Dacetylan/FLWSB/docs/demo/flwsb-demo.md

# DEMO

## FLWSB

Demo opstelling van de SAMDaaNo21 PoC met BME280 breakoutboard op breadboard.
Gevoed door de Solar Power Manager met twee kleine zonnepanelen en heroplaadbare Li-Po batterij.

### Overzicht

FLWSB demo opstellig: overzicht, hoek. Figuur 1: FLWSB demo opstellig: overzicht, hoek..

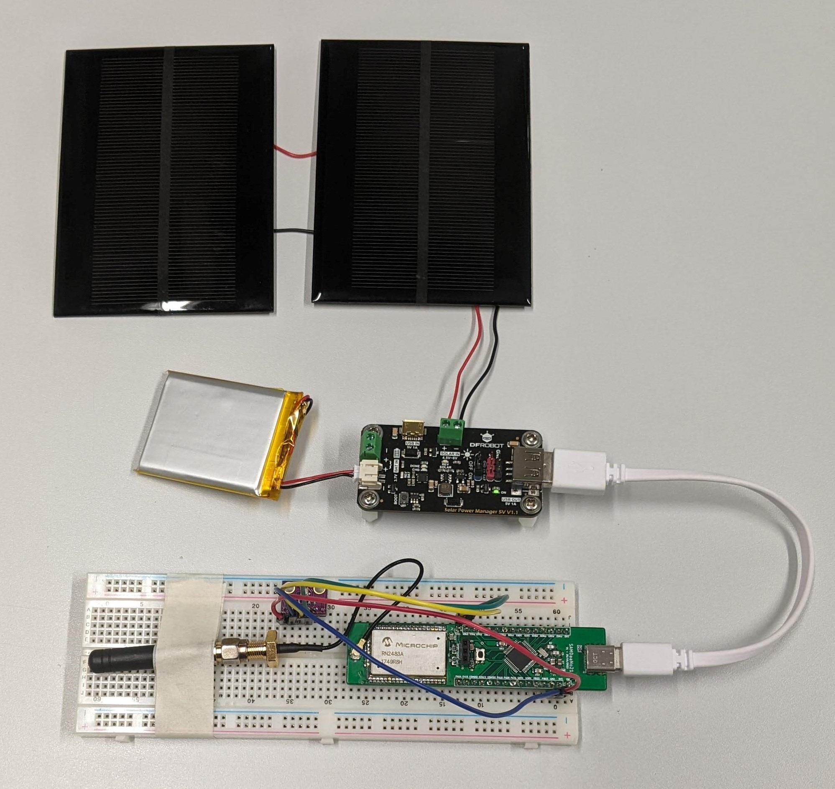
[picture p45: docs/demo/assets/flwsb-demo-overview-top.jpg]
FLWSB demo opstellig: overzicht, bovenaanzicht. Figuur 2: FLWSB demo opstellig: overzicht, bovenaanzicht..


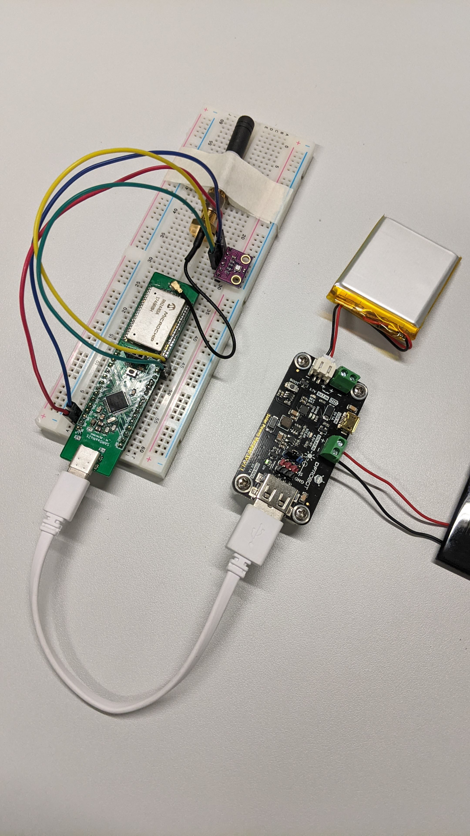
[picture p46: docs/demo/assets/flwsb-demo-overview-woSolar-angle.jpg]
FLWSB demo opstellig: overzicht, hoek, zonder zonnepanelen. Figuur 3: FLWSB demo opstellig: overzicht, hoek, zonder zonnepanelen..


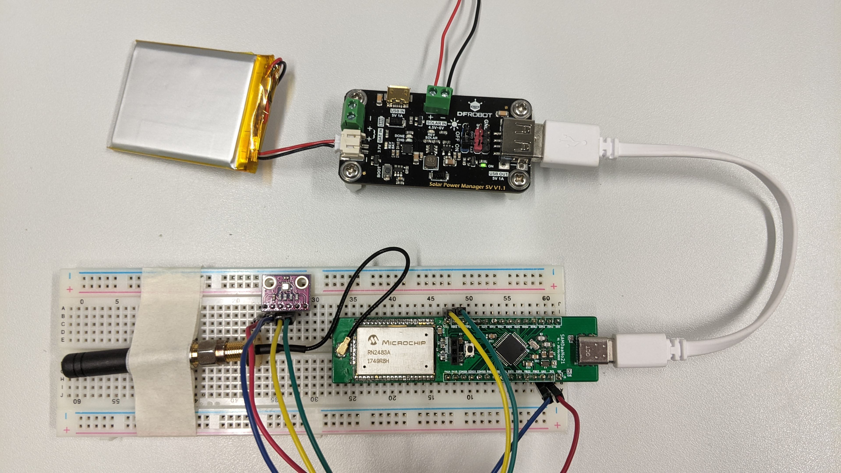
[picture p47: docs/demo/assets/flwsb-demo-overview-woSolar-top.jpg]
FLWSB demo opstellig: overzicht, top, zonder zonnepanelen. Figuur 4: FLWSB demo opstellig: overzicht, top, zonder zonnepanelen..


### Solar Power Manager met Li-Po batterij en zonnepanelen

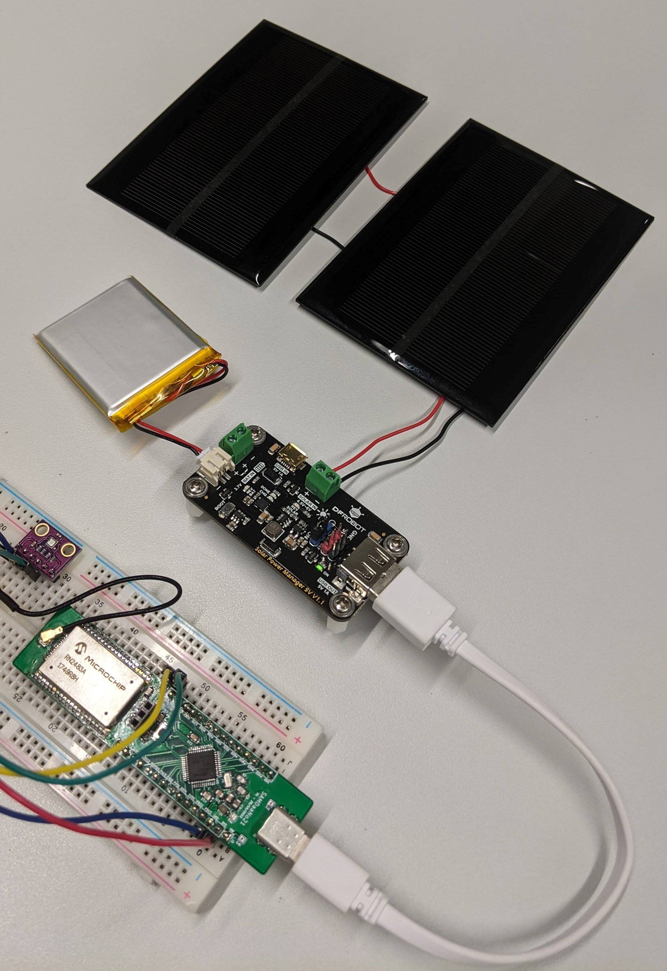
[picture p48: docs/demo/assets/flwsb-demo-solar-angle.jpg]
FLWSB demo opstellig: Solar Power Manager met Li-Po batterij en zonnepanelen, hoek. Figuur 5: FLWSB demo opstellig: Solar Power Manager met Li-Po batterij en zonnepanelen, hoek..


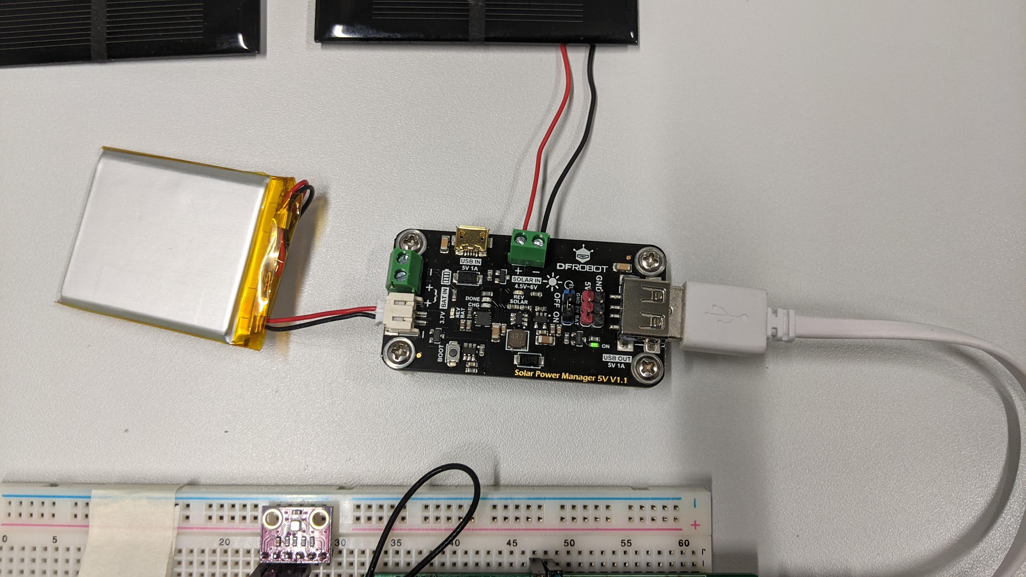
[picture p49: docs/demo/assets/flwsb-demo-solar-top.jpg]
FLWSB demo opstellig: Solar Power Manager met Li-Po batterij en zonnepanelen, bovenaanzicht. Figuur 6: FLWSB demo opstellig: Solar Power Manager met Li-Po batterij en zonnepanelen, bovenaanzicht..


### SAMDaaNo21

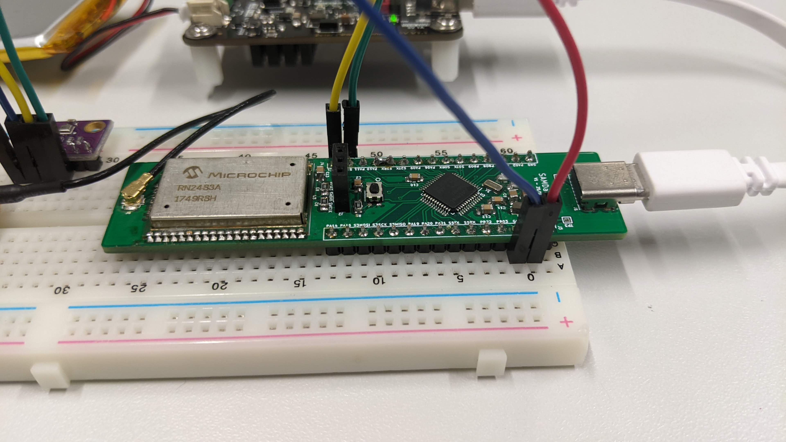
[picture p50: docs/demo/assets/flwsb-demo-samdaano21-close-up-side.jpg]
FLWSB demo opstellig: SAMDaaNo21, zijdelinks. Figuur 7: FLWSB demo opstellig: SAMDaaNo21, zijdelinks..


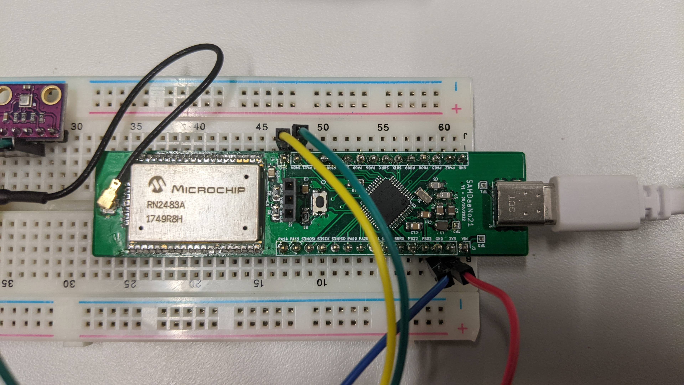
[picture p51: docs/demo/assets/flwsb-demo-samdaano21-close-up-top.jpg]
FLWSB demo opstellig: SAMDaaNo21, bovenaanzicht. Figuur 8: FLWSB demo opstellig: SAMDaaNo21, bovenaanzicht..


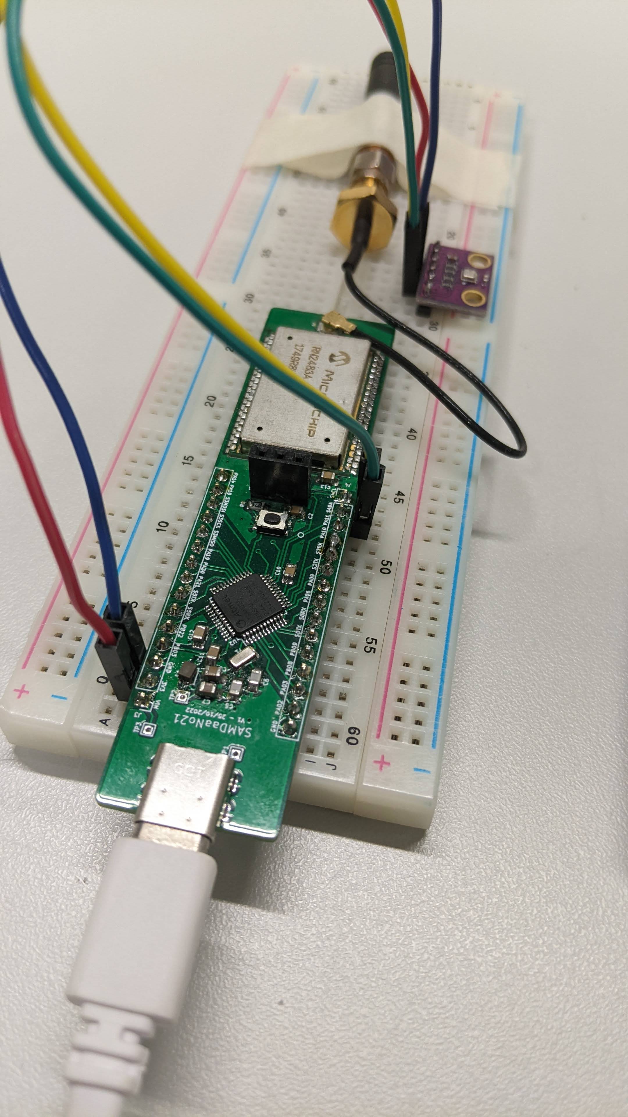
[picture p52: docs/demo/assets/flwsb-demo-samdaano21-close-up-angle.jpg]
FLWSB demo opstellig: SAMDaaNo21, hoek. Figuur 9: FLWSB demo opstellig: SAMDaaNo21, hoek..


### BME280 breakoutboard

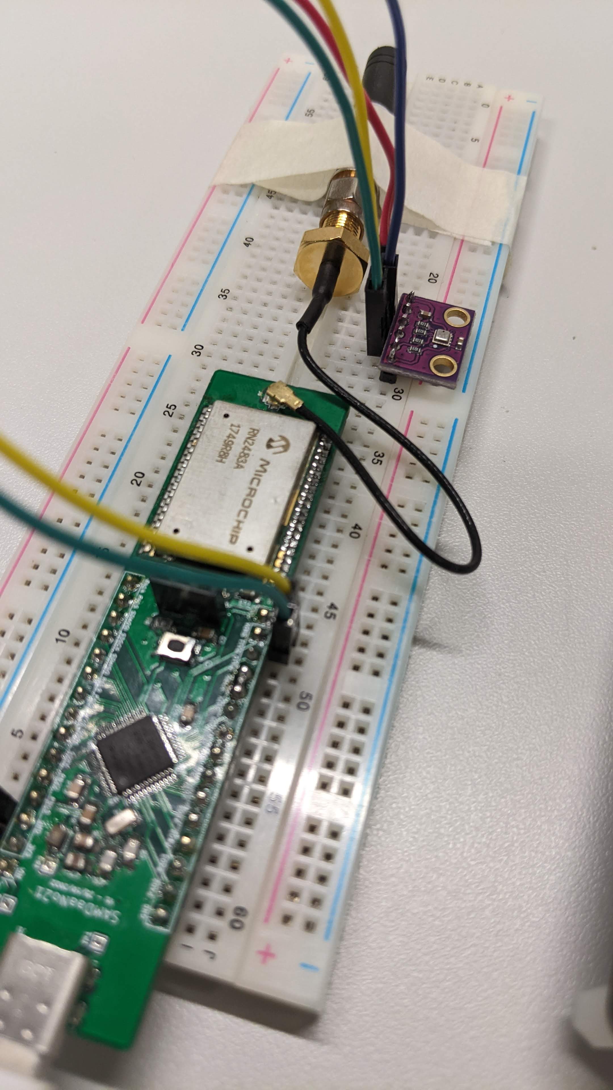
[picture p53: docs/demo/assets/flwsb-demo-bme280-close-up-angle.jpg]
FLWSB demo opstellig: BME280 breakoutboard, hoek. Figuur 10: FLWSB demo opstellig: BME280 breakoutboard, hoek..


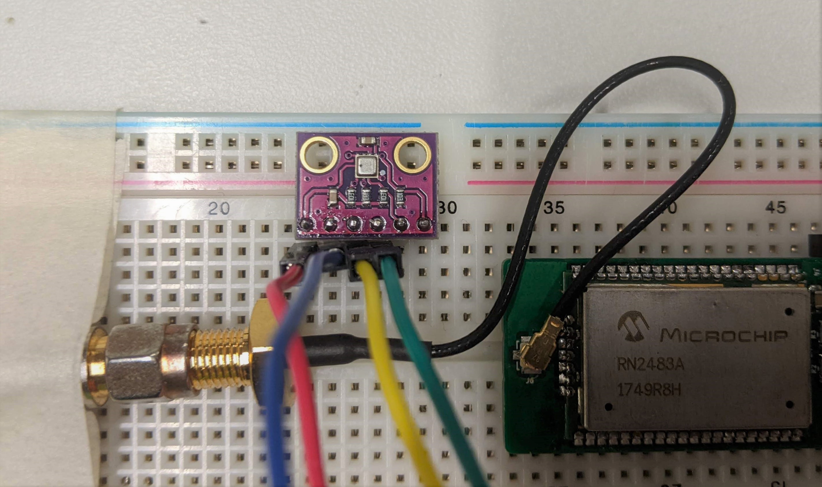
[picture p54: docs/demo/assets/flwsb-demo-bme280-close-up-top.jpg]
FLWSB demo opstellig: BME280 breakoutboard, bovenaanzicht. Figuur 11: FLWSB demo opstellig: BME280 breakoutboard, bovenaanzicht..
