Dacetylan/FLWSB/docs/enclosure/considerations.md

# Behuizing

## Overwegingen

### Introductie

De behuizing zelf is geen onderdeel van deze itteratie van het project. Bij het ontwikkelen van de PCB's is het echter belangrijk al na te denken over hoe deze geplaatst zal worden. Zeker omdat het doel is om dit project uit te rollen in Sub-Sahara Afrika wat een zeer andere omgeving is als West-Europa. Meer specifiek in Zanzibar, Tanzania en Ghana.

Er zal gebruik gemaakt worden van __zonne-energie__ aan de hand van zonnepanelen waar een aantal factoren bij komen kijken.
Factoren waarbij er rekening moet gehouden worden bij het plaatsen van zonne-panelen in Sub-Sahara Afrika:
- Kantelhoek (tilt angle) van het zonnepaneel
- Oriëntatie van het zonnenpaneel
- Afzetting van Harmattan dust
- Afwatering van regenwater
- Temperatuur van het zonnenpaneel

Andere factoren waar rekening mee gehouden moet worden zijn algemen zaken bij het opmeten van __klimatologische data__ zoals:
- Lucht toe voer naar sensoren voor lucht en deeltjes analyse.
- Stof filtering van grote stofdeeltjes groter dan 10 micron.
- Invloed van opwarmende componenten voor temperatuur metingen en dus koeling.
- Afdekking van de elektronica tegen vocht en regen.

In dit hoofdstuk worden deze factoren verder besproken.
