Dacetylan/FLWSB/docs/enclosure/measuring-climate.md

# Behuizing

## Klimatologische metingen

Voor het meten van klimatologische data moet er rekening gehouden worden met een aantal factoren zoals:
- Lucht toe voer naar sensoren voor lucht en deeltjes analyse.
- Stof filtering van grote stofdeeltjes groter dan 10 micron.
- Invloed van opwarmende componenten voor temperatuur metingen en dus koeling.
- Afdekking van de elektronica tegen vocht en regen.

### Stevenson Screen

### Bestaande behuizingen

#### Off-the-shelf behuizingen

#### 3D Printing
