Dacetylan/FLWSB/docs/frontend/Documentatie Frontend.md

# Documentatie Frontend

### Mock up

Voor dat het mogelijk is om te beginnen met het ontwerpen van de frontend moet er een mock up gemaakt worden. Voor de frontend zijn er twee onderdelen. Een Sensor Registration Form en een grafische weergave van de data.

Screenshot 2022-09-30 at 11.58.03.png

*fig. 1, Sensor Registration Form Mock up*



*fig. 2, Grafana wordt gebruikt voor een grafische weergave van de data*

### Sensor Registration Form

De eerste versie van de Sensor Registration Form werd ontworpen met Angular. Angular werd gebruik omdat dit de techniek is dat aangeleerd werd tijdens de lessen Web Frameworks.

Screenshot 2022-10-28 at 10.28.20.png

*fig. 3, eerste versie Sensor Regiostration Form*

Angular is heel inefficiënt en eigenlijk helemaal niet leuk om mee te werken. We hebben voor de tweede versie besloten om gebruik te maken van NodeRED Dashboard voor de Sensor Registration Form. NodeRED wordt al gebruikt voor de backend. Zo moeten we geen nieuwe Docker container opstarten voor een simpele form. Deze tweede versie is nog niet gebouwd.
