Dacetylan/FLWSB/docs/backend/influxdb.md

# Backend

## InfluxDb Time-Series Database

Voor dit project is er gekozen om te werken met InfluxDb.
Dit is een time-series database, wat wilt zeggen dat aan alle datapunten een timestamp, of datum en tijdstip is gekoppeld. Dit maakt het uitermate geschikt om historische data te verzamelen en deze om te zetten in grafieken. Ideaal dus voor klimatologische data zoals in dit project.

De keuze voor deze database ligt ook bij onze keuze voor het gebruik van Grafana als frontend visualisatie van de verzamelde data. Grafana beschikt over een eenvoudige, en gratis, plug-in die de verbinding tussen de twee super simpel maakt om op te zetten.

Enkele specificaties:
- InfluxDb 2.0
- Open-source Time Series Database (TSDB)
- geschreven in GO programeertaal
- Flux query-taal

[Officiële documentatie website](https://www.influxdata.com/_resources/)

Voordelen:
- Zeer performant in queriën van zeer grote hoeveelheden data.
- Wanneer geschreven wordt naar de database werkt dit het beste in grote blokken data in één keer.
- Zeer eenvoudig data op te vragen door schema systeem (zie Schema Design onderaan) met tags.

---

### Werking

InfluxDb beschikt over een CLI, maar kan ook eenvoudig beheerd worden aan de hand een web interface.

#### Buckets

Buckets zijn eenvoudig te beheren.

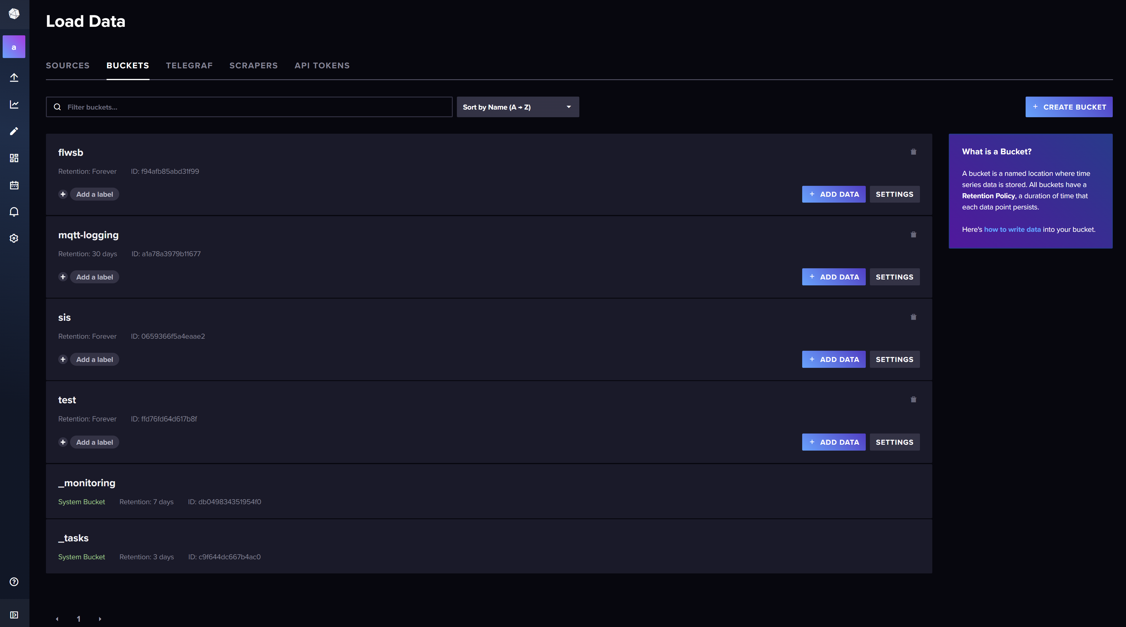
[picture p68: docs/backend/assets/influxdb-buckets.png]
InfluxDb web interface: Buckets. Figuur 1: InfluxDb web interface: Buckets.


#### API Tokens

API tokens aanmaken, om connecties naar buiten op te zetten, met specifieke machtigingen kunnen ook zeer eenvoudig.

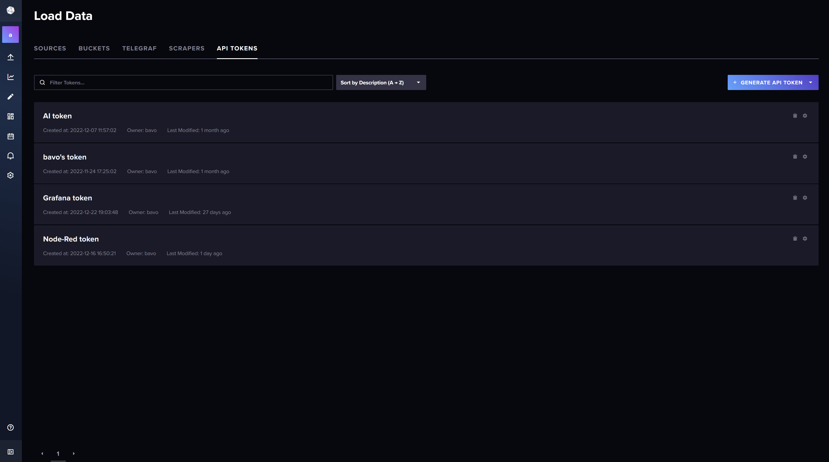
[picture p69: docs/backend/assets/influxdb-api-tokens.png]
InfluxDb web interface: API tokens. Figuur 2: InfluxDb web interface: API tokens.


#### Data Explorer

De web interface beschikt ook over een Data Explorer. Een zeer handige tool om query's op te stellen, als ook een snelle visualisatie van data.

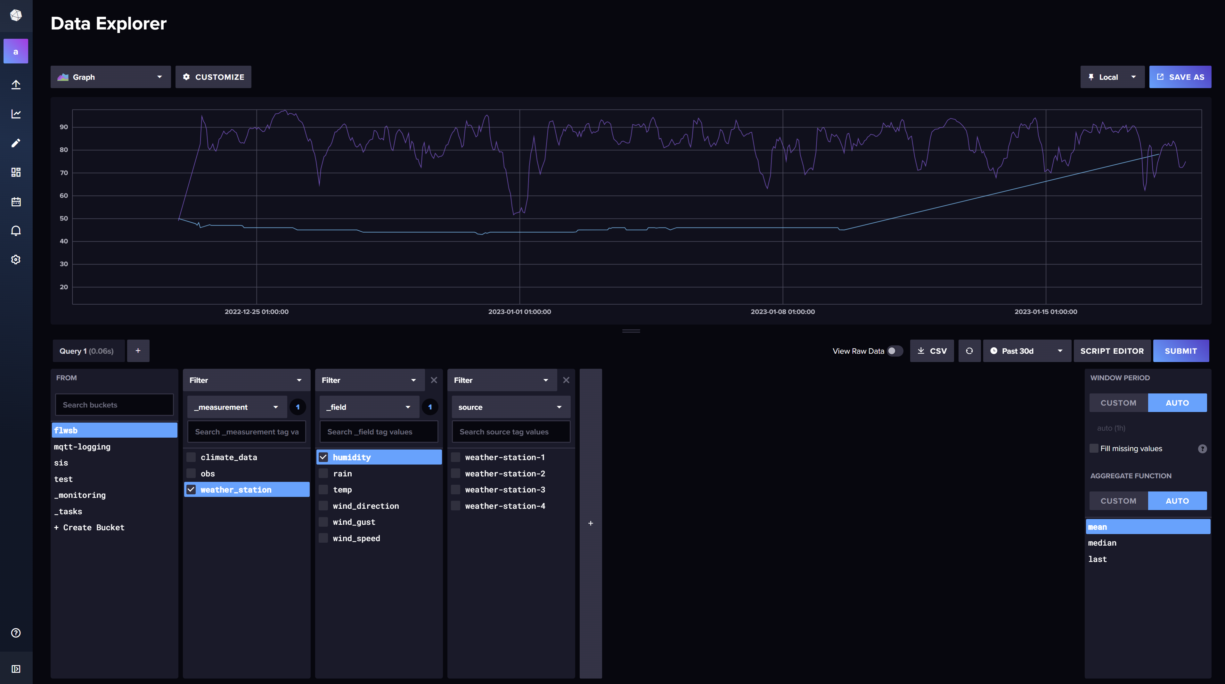
[picture p70: docs/backend/assets/influxdb-data-explorer-query-builder-graph.png]
InfluxDb web interface: Data Explorer, Query Builder en graph view. Figuur 3: InfluxDb web interface: Data Explorer, Query Builder en graph.


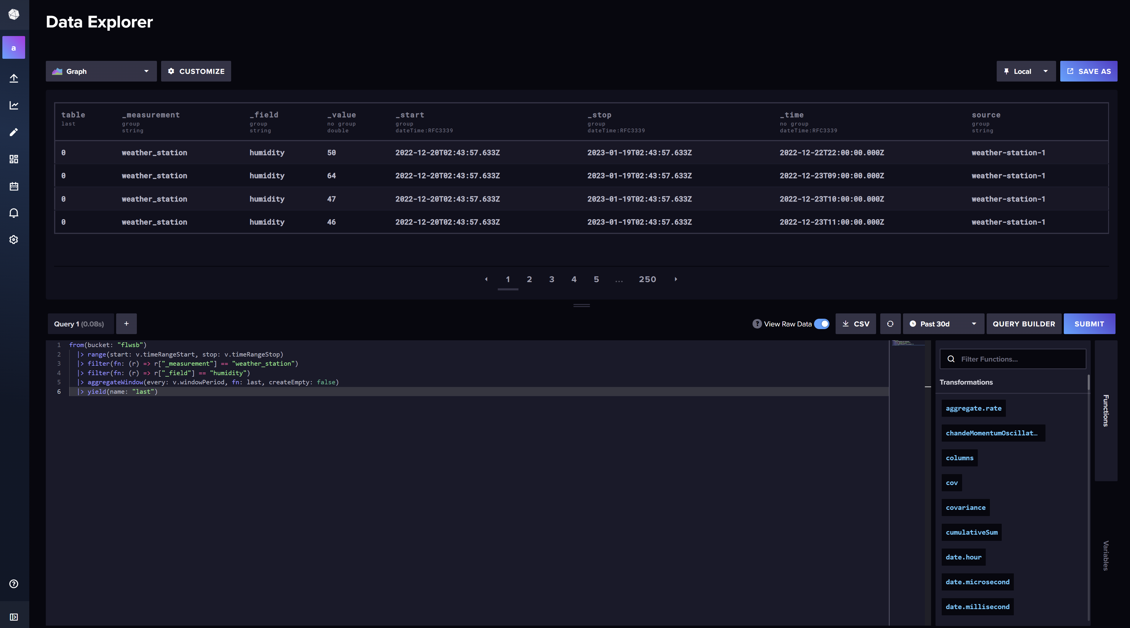
[picture p71: docs/backend/assets/influxdb-data-explorer-script-editor-raw-data.png]
InfluxDb web interface: Data Explorer, Script Editor en raw data view. Figuur 4: InfluxDb web interface: Data Explorer, Script Editor en raw data view.


---

### Schema Design

De InfluxDb documentatie heeft een onderdeel over InfluxDb schema design onder [Write data - Best practices- Schema design](https://docs.influxdata.com/influxdb/v2.4/write-data/best-practices/schema-design/).

InfluxDb bestaat uit volgende onderdelen:

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

_**Keys** herhalen niet binnen een schema en kunnen geen gereserveerde keywords zijn of speciale tekens bevatten._

_**Measurements** en **keys** bevatten geen data; **tag values** en **field values** bevatten wel data._

_Een **datapunt / point** bevat een series key, een field value en een timestamp.
vb. ```2019-08-18T00:00:00Z census ants 30 portland mullen```. Waarbij measurement = census, field key = ants, field value = 30, location tag = portland, en scientist tag = mullen._

_Een **series key** is een collectie van datapunten dat een measurement, tag set en field key delen.
Een **series** bevat timestamps en field values voor een bepaalde series key._

[_Bron: InlfuxDb data elements_](https://docs.influxdata.com/influxdb/cloud/reference/key-concepts/data-elements/#bucket)

<br>
