Dacetylan/FLWSB/docs/frontend/dashboard.md

# Frontend

## Node-RED Dashboard

Als invoer manier voor het Sensor Identification System (SIS) wordt er gebruik gemaakt van Node-RED Dashboard. Dit genereerd een eenvoudige web pagina met de nodige formulieren.
De werking hiervan is gedocumenteerd in het onderdeel [Node-RED](backend/nodered.md) onder Backend.

SIS Registration Form webpagina. Figuur 1: SIS Registration Form webpagina.

Met voorbeeld data ingevuld:

SIS web forms voorbeeld. Figuur 2: SIS web forms voorbeeld.
