Dacetylan/FLWSB/docs/demo/weather-station-demo.md

# DEMO

# Weerstation

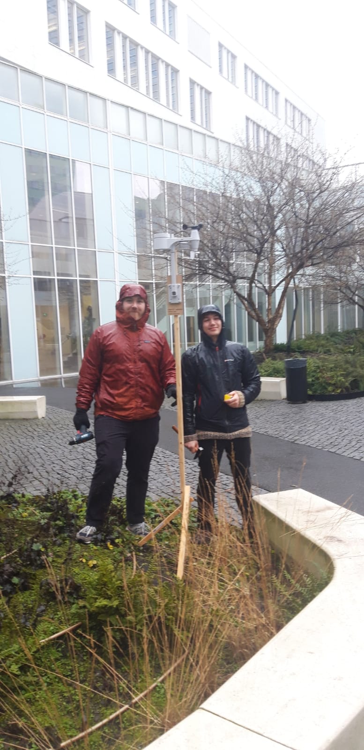
[picture p80: docs/demo/assets/weather-station-demo-birk-luyts.jpeg]
Buiten opstelling van demo weerstation met Maarten Luyts links en Birk Tamm rechts, dag 1. Figuur 1: Buiten opstelling van demo weerstation met Maarten Luyts links en Birk Tamm rechts, dag 1.


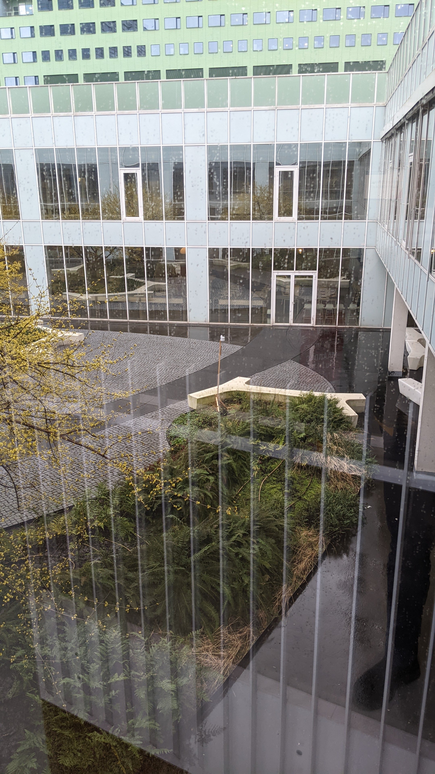
[picture p81: docs/demo/assets/weather-station-demo-1.jpg]
Buiten opstelling van demo weerstation, een maand later. Figuur 2: Buiten opstelling van demo weerstation, een maand later.


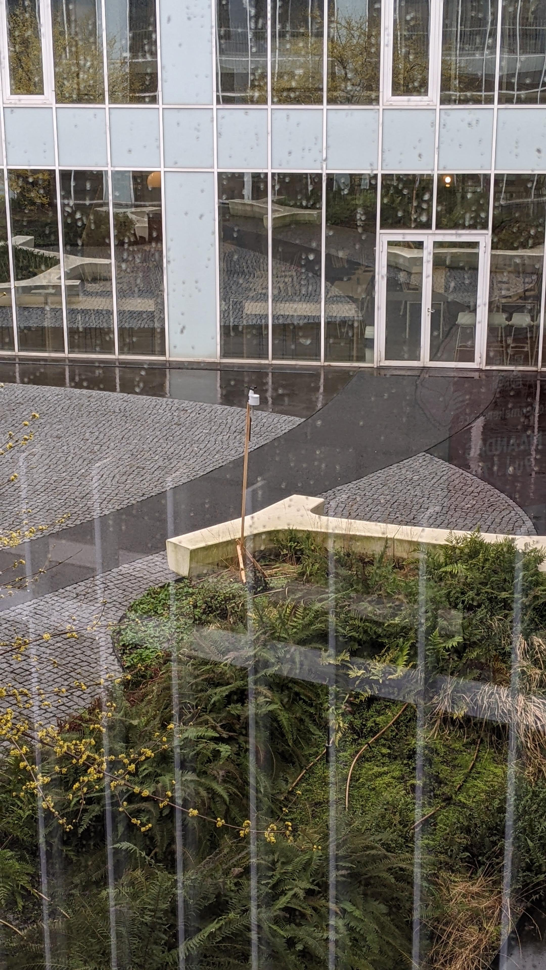
[picture p82: docs/demo/assets/weather-station-demo-2.jpg]
Buiten opstelling van demo weerstation, een maand later (zoom). Figuur 3: Buiten opstelling van demo weerstation, een maand later (zoom).


Buiten opstelling van demo weerstation, een maand later (extra zoom). Figuur 4: Buiten opstelling van demo weerstation, een maand later (extra zoom).
