Dacetylan/FLWSB/docs/backend/assets/grafana-dashboard-weather-stations.png

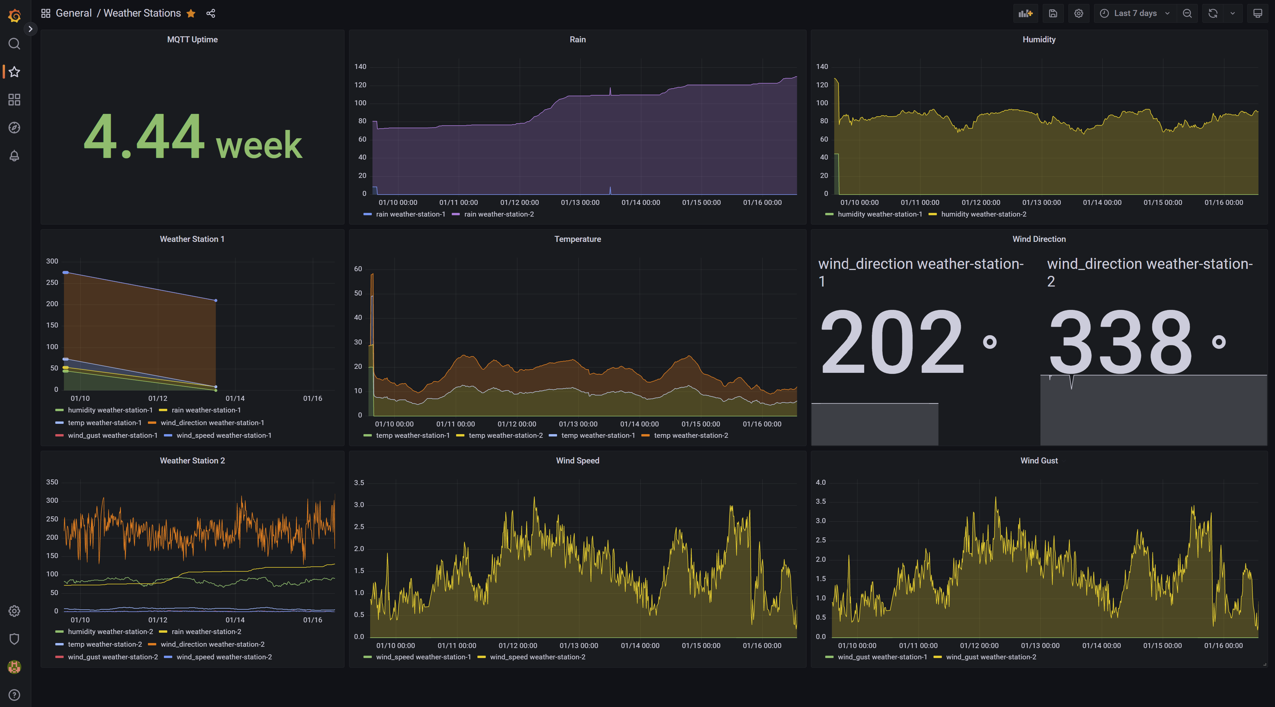
docs/backend/assets/grafana-dashboard-weather-stations.png
