Dacetylan/FLWSB/docs/backend/assets/ttn-collaborators.png

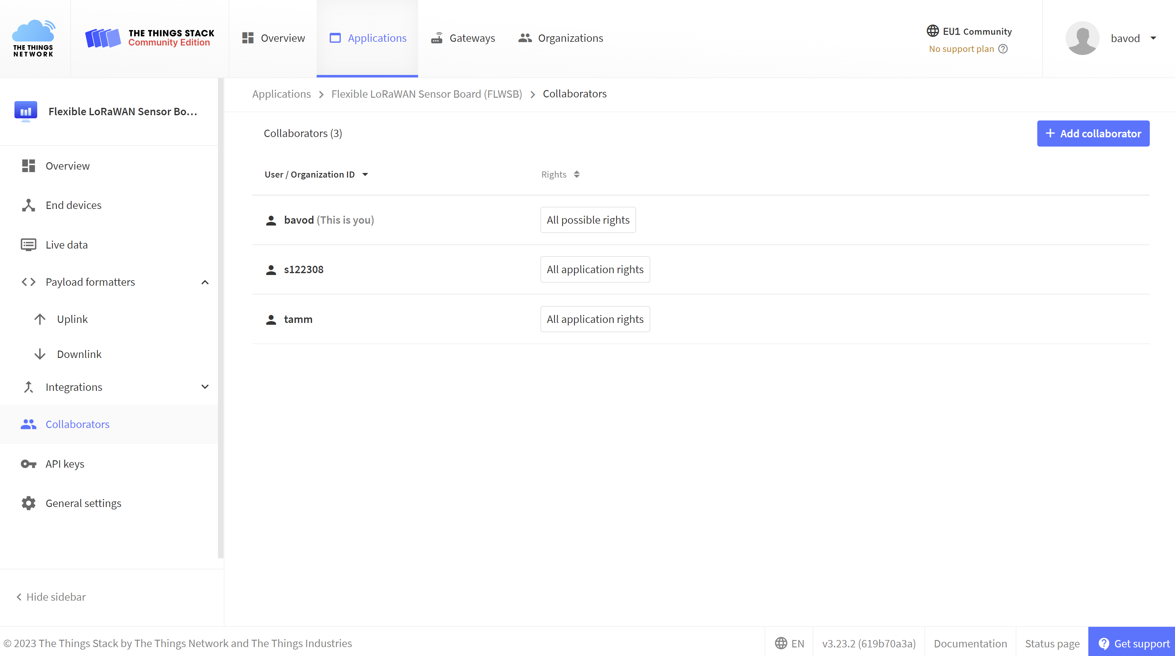
docs/backend/assets/ttn-collaborators.png
