Dacetylan/FLWSB/docs/backend/assets/ttn-id.png

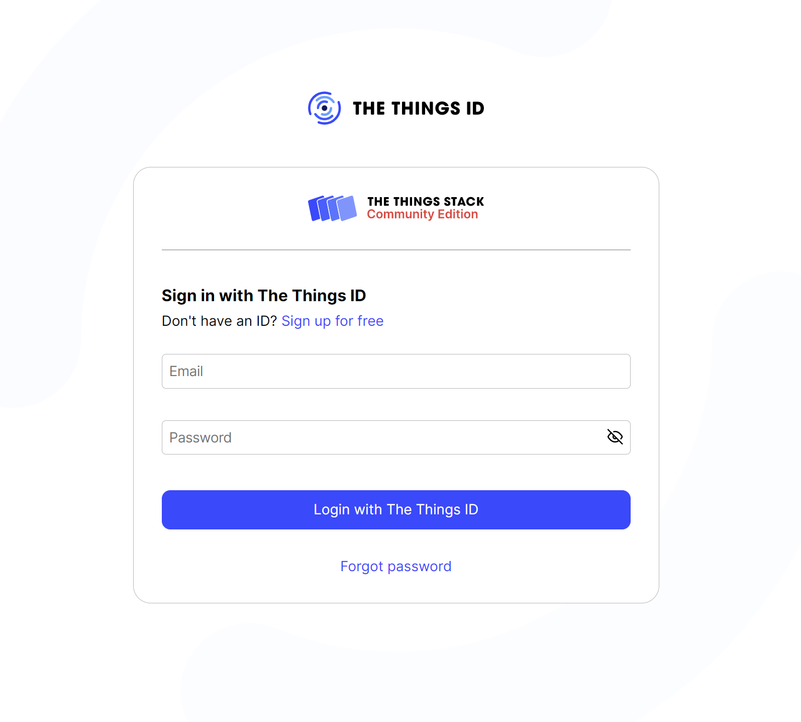
docs/backend/assets/ttn-id.png
