Dacetylan/FLWSB/docs/data-formatting/assets/node-red-flow-ttn-flwsb.png

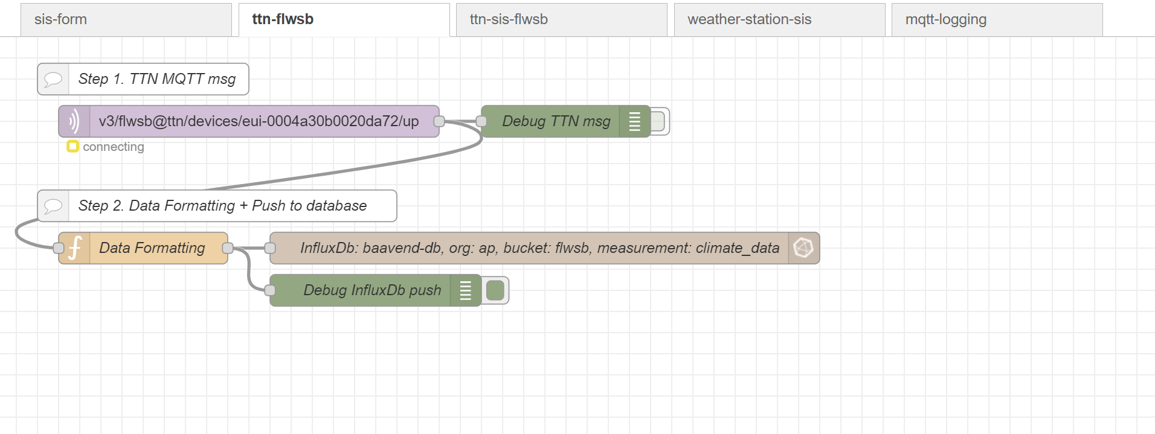
docs/data-formatting/assets/node-red-flow-ttn-flwsb.png
