Dacetylan/FLWSB/docs/data-formatting/assets/node-red-flow-weather-station.png

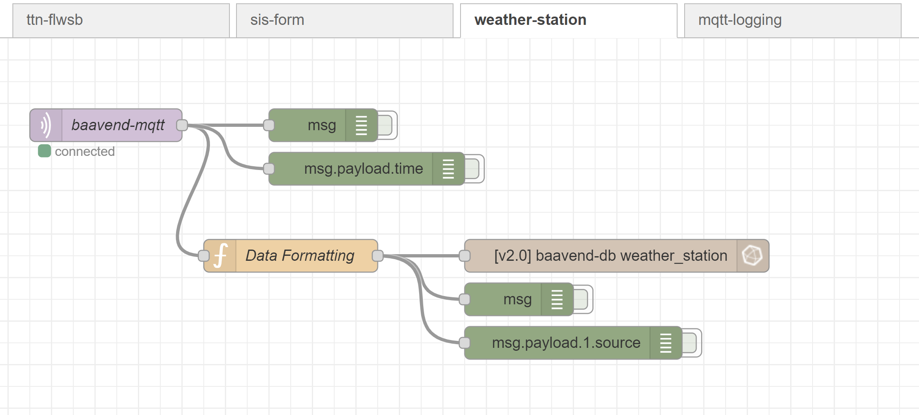
docs/data-formatting/assets/node-red-flow-weather-station.png
