Dacetylan/FLWSB/docs/data-formatting/assets/zanzibar/formatted-msg.png

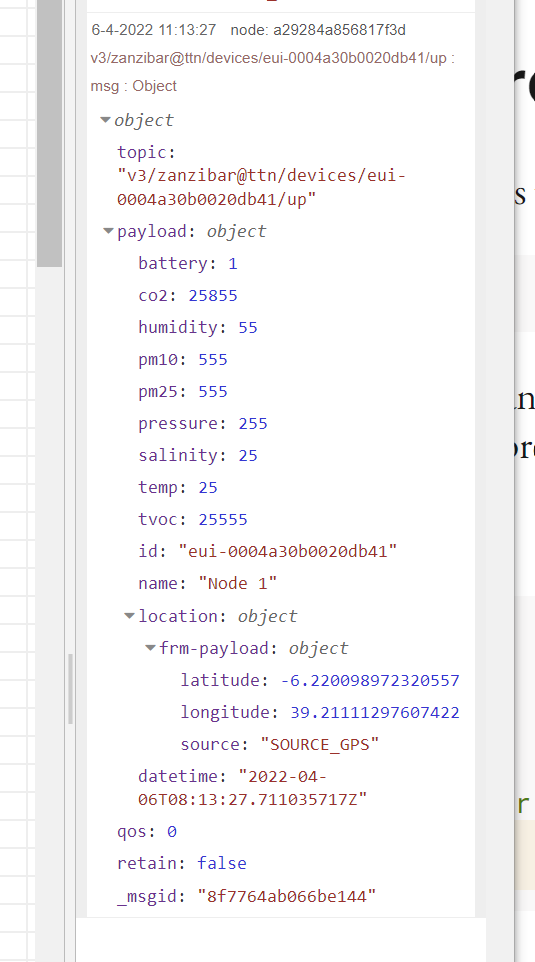
docs/data-formatting/assets/zanzibar/formatted-msg.png
