Dacetylan/FLWSB/docs/data-formatting/assets/zanzibar/node-red-function-full.png

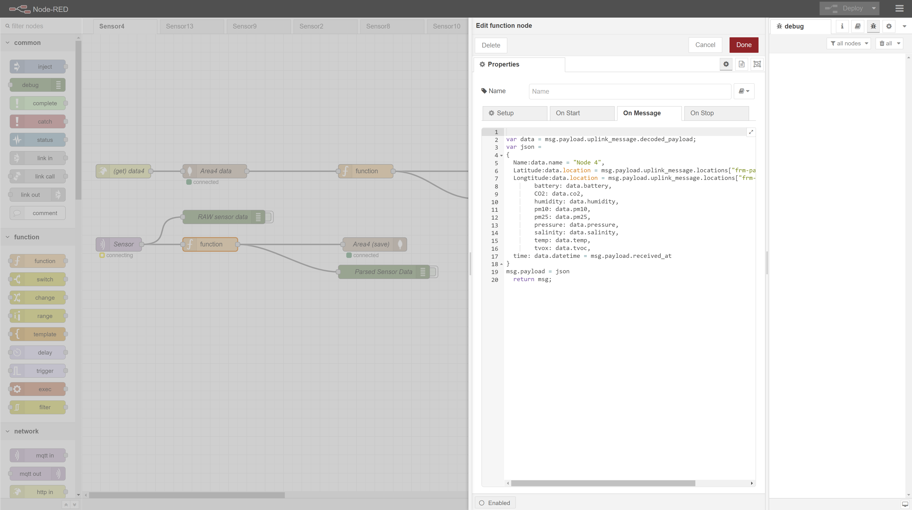
docs/data-formatting/assets/zanzibar/node-red-function-full.png
