Dacetylan/FLWSB/docs/data-formatting/assets/zanzibar/node-red-function.png

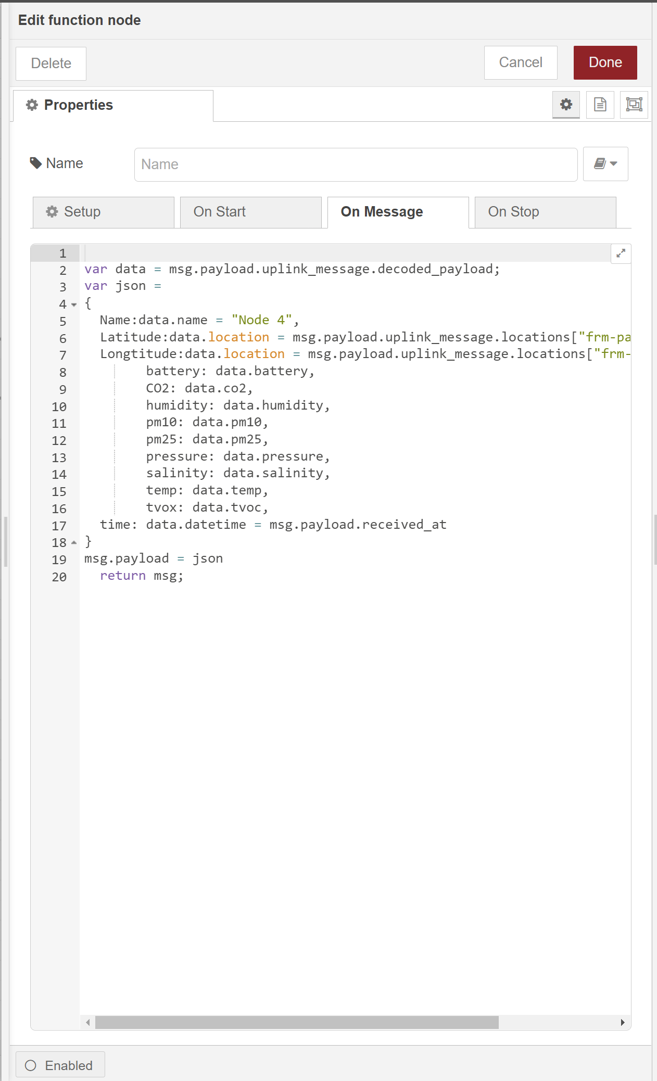
docs/data-formatting/assets/zanzibar/node-red-function.png
