Dacetylan/FLWSB/docs/data-formatting/assets/zanzibar/node-red-incoming-and-parsed-data-full.png

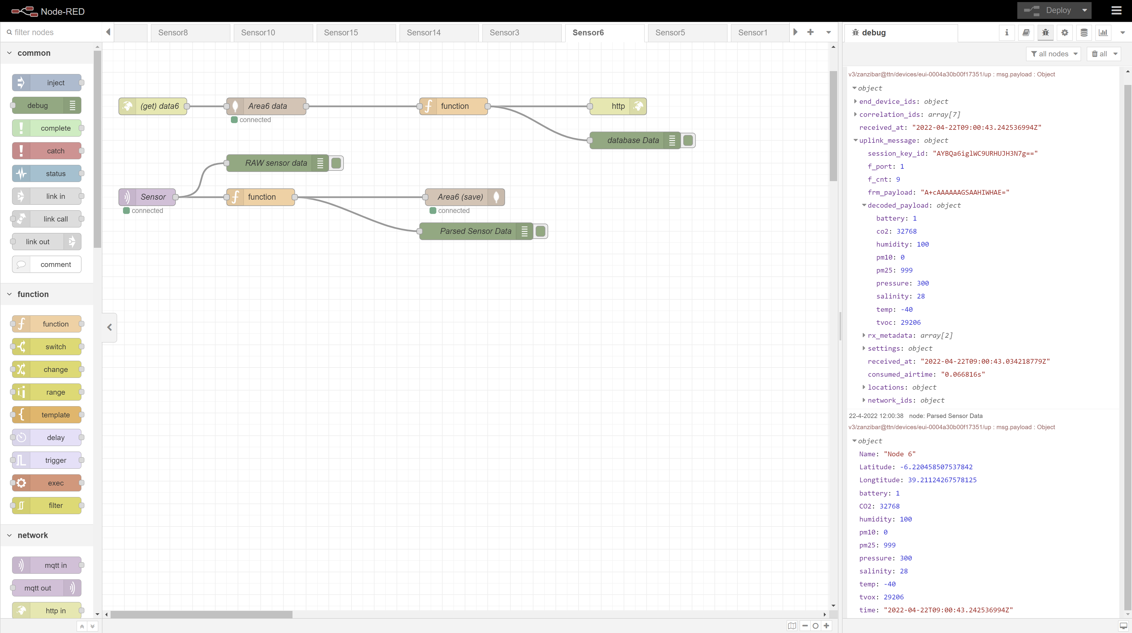
docs/data-formatting/assets/zanzibar/node-red-incoming-and-parsed-data-full.png
