Dacetylan/FLWSB/docs/data-formatting/assets/zanzibar/node-red-incoming-and-pasred-data.png

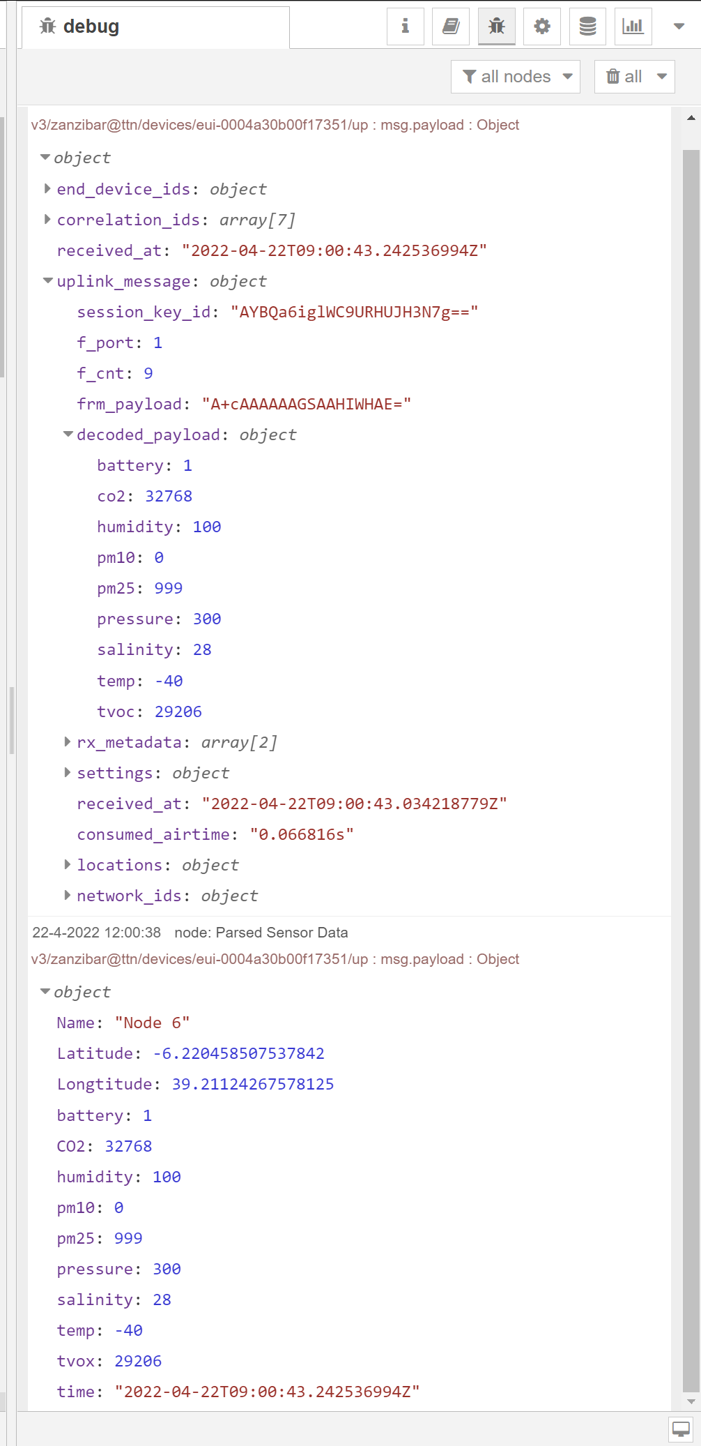
docs/data-formatting/assets/zanzibar/node-red-incoming-and-pasred-data.png
