Dacetylan/FLWSB/docs/data-formatting/assets/zanzibar/ttn-payload-formatter.png

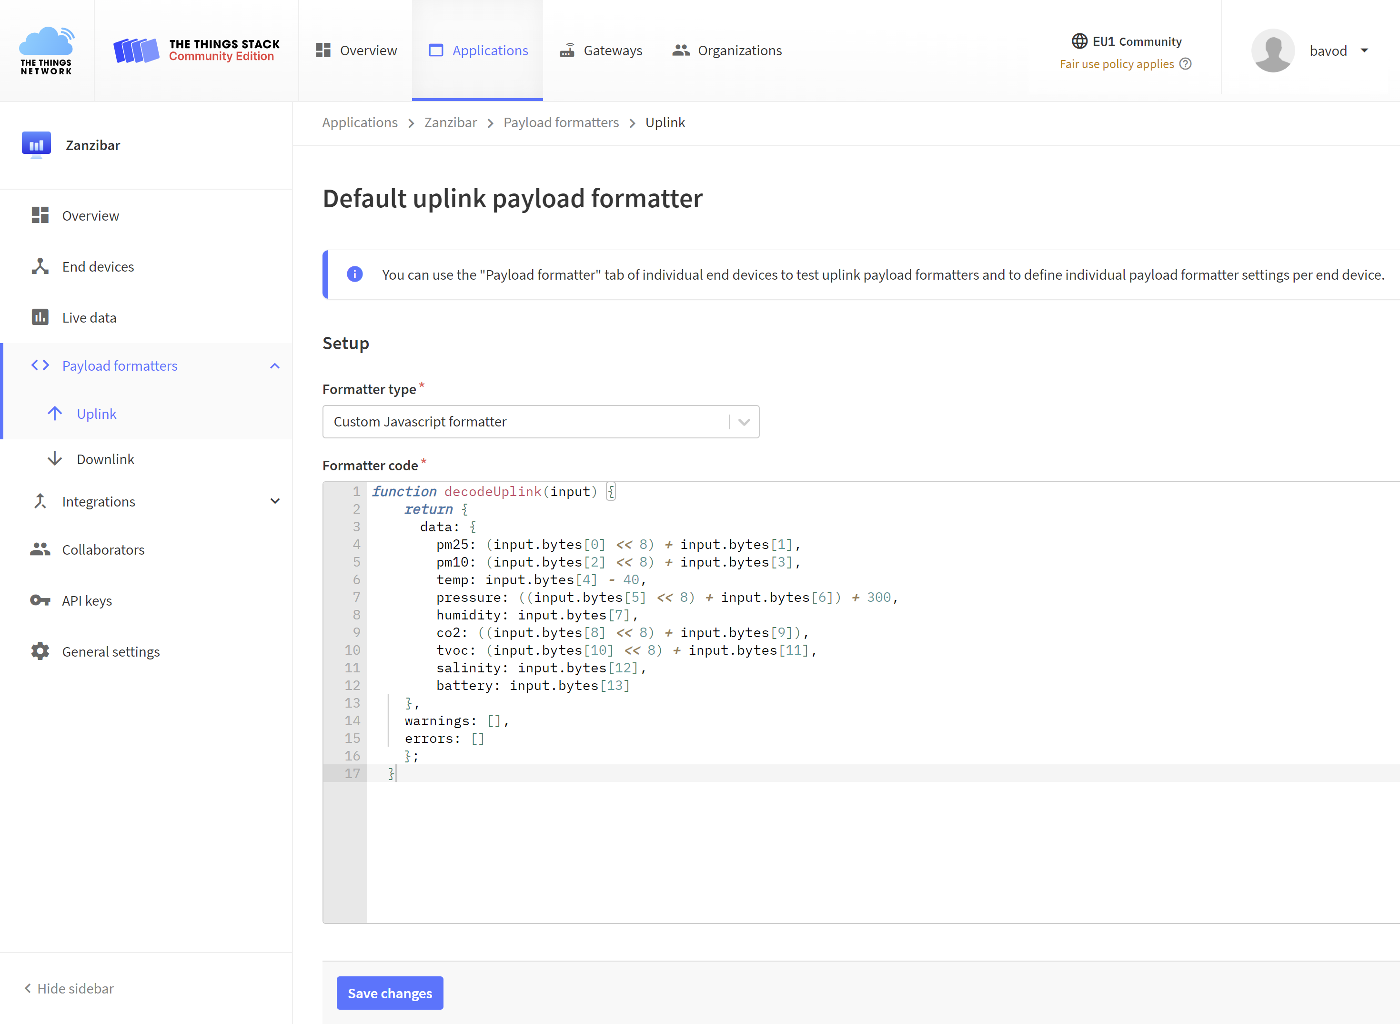
docs/data-formatting/assets/zanzibar/ttn-payload-formatter.png
