Dacetylan/FLWSB/docs/enclosure/assets/solar-power-optimal-angle.webp

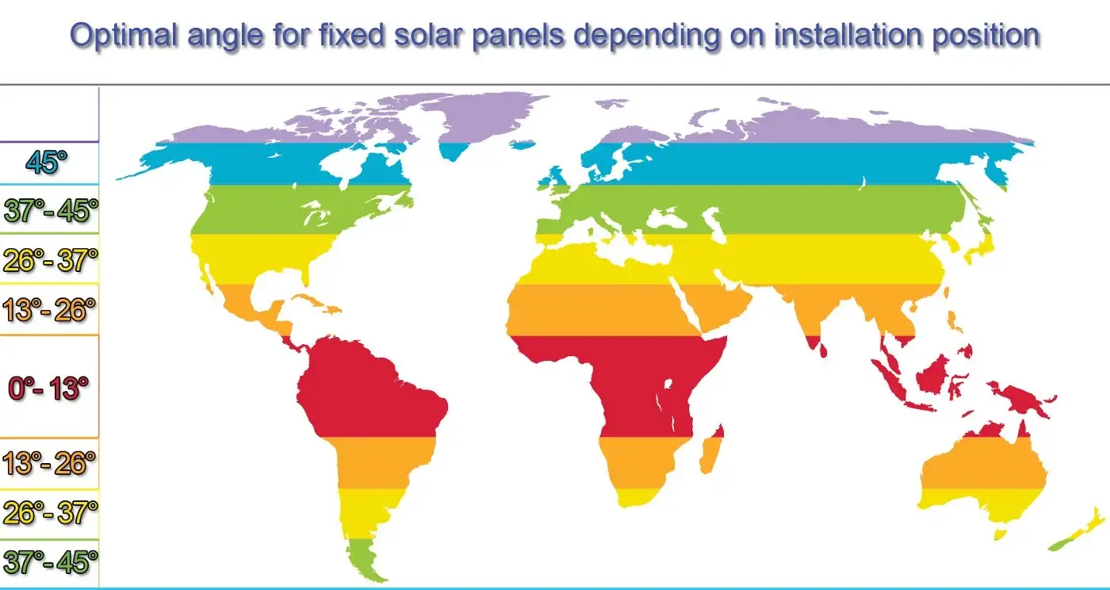
docs/enclosure/assets/solar-power-optimal-angle.webp
