Dacetylan/FLWSB/docs/flexibility/assets/sensoren/DHT22-breakout.png

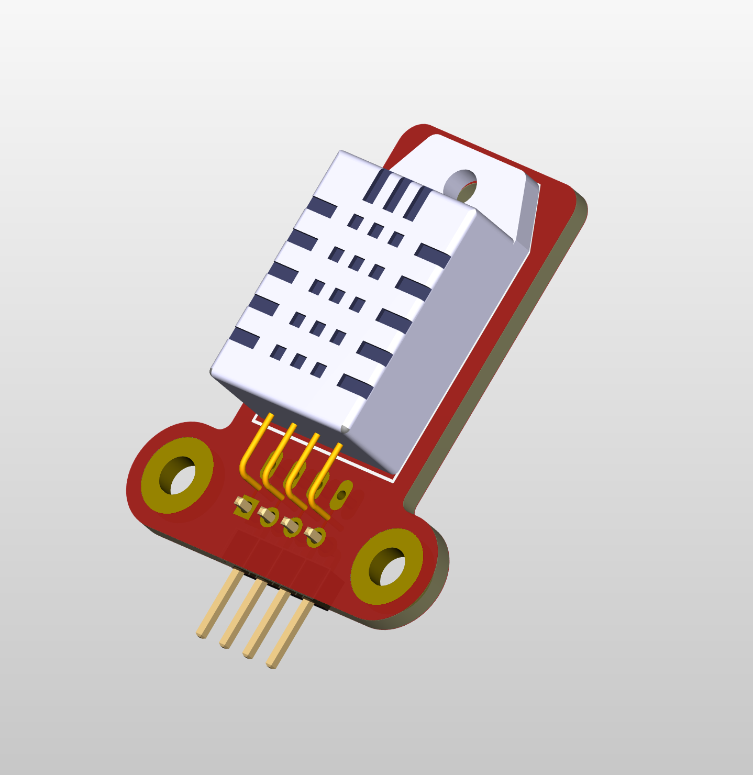
docs/flexibility/assets/sensoren/DHT22-breakout.png
