Dacetylan/FLWSB/docs/flexibility/assets/sensoren/GY-NEO6MV2-breakoutboard.jpg

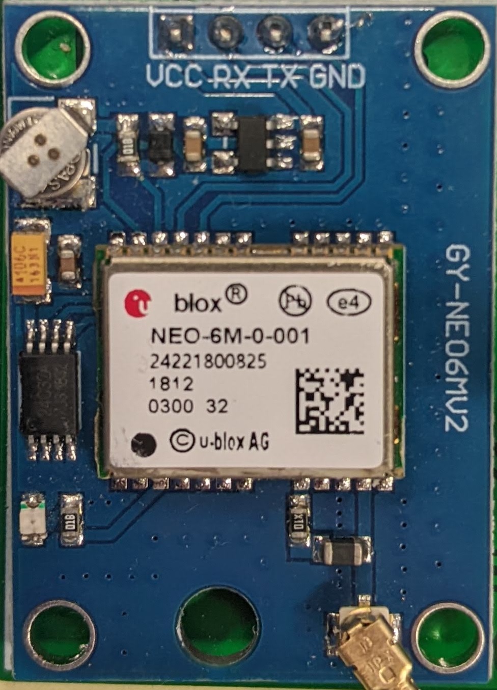
docs/flexibility/assets/sensoren/GY-NEO6MV2-breakoutboard.jpg
