Dacetylan/FLWSB/docs/flexibility/assets/sensoren/SCD41-breakoutboard.jpg

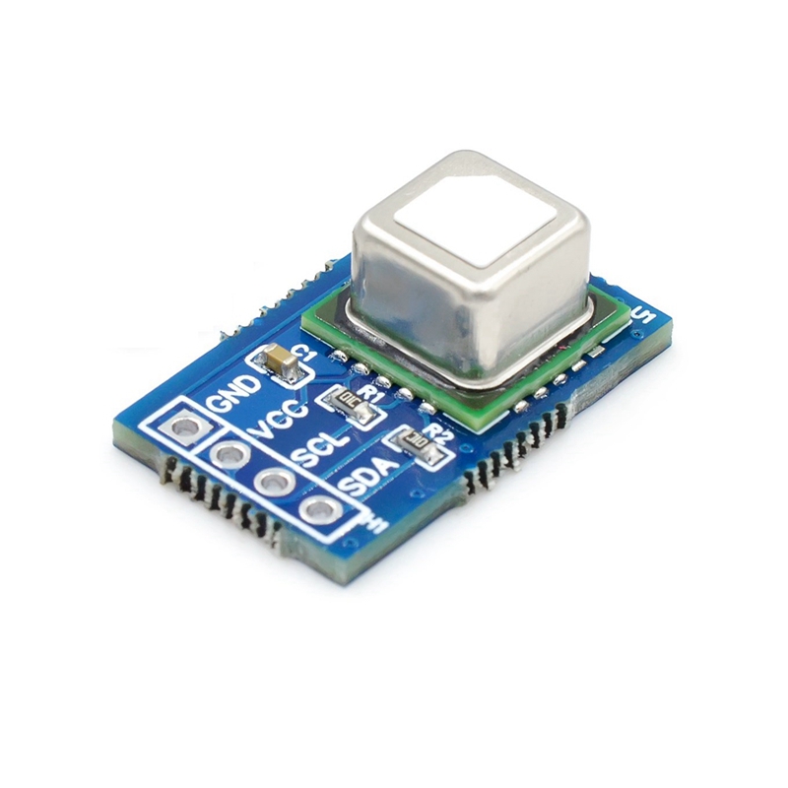
docs/flexibility/assets/sensoren/SCD41-breakoutboard.jpg
