Dacetylan/FLWSB/docs/flexibility/assets/sensoren/SCD41-interface-specs.png

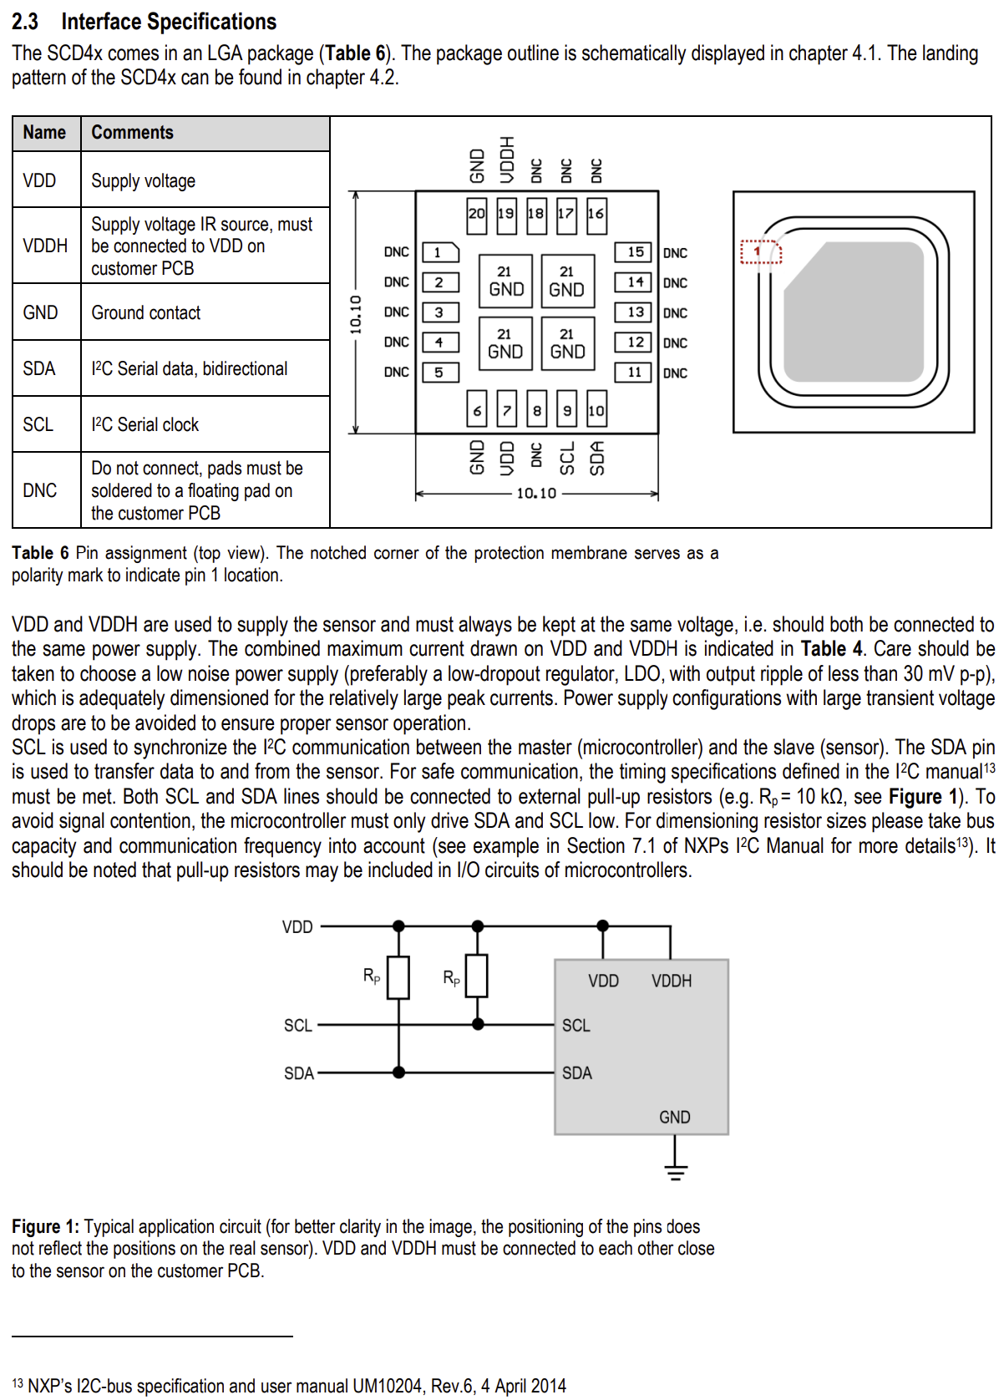
docs/flexibility/assets/sensoren/SCD41-interface-specs.png
