Dacetylan/FLWSB/docs/flexibility/assets/sensoren/SGP41-breakoutboard.jpg

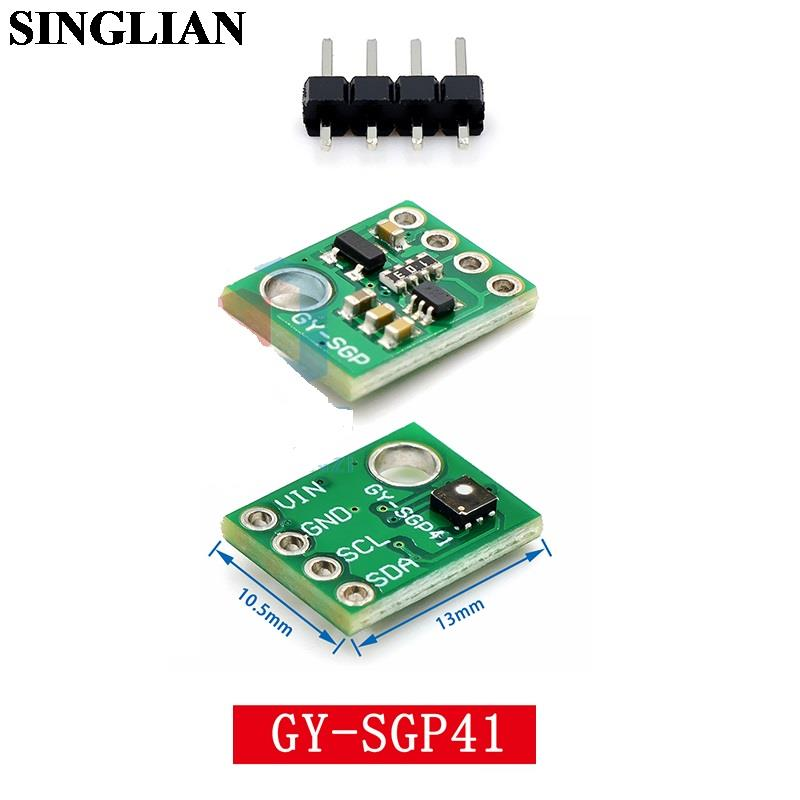
docs/flexibility/assets/sensoren/SGP41-breakoutboard.jpg
